MonisRaza123/balloon_driver/images/enclosure2.jpg

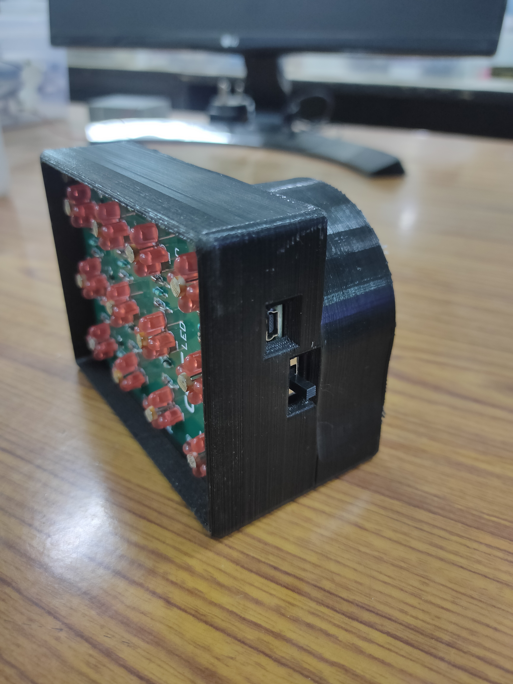
images/enclosure2.jpg
