MonisRaza123/balloon_driver/images/IMG20230621204712.jpg

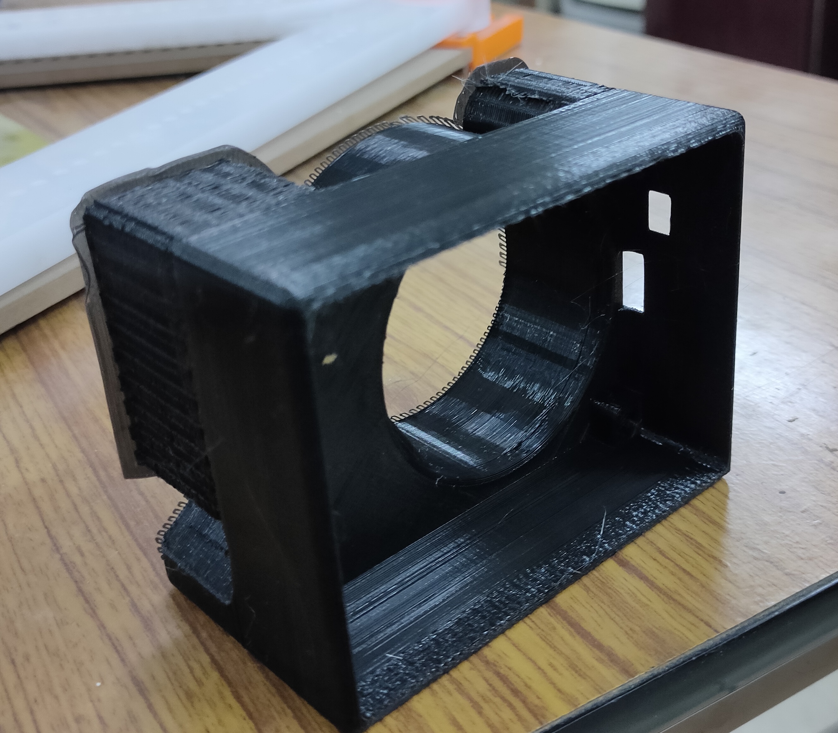
images/IMG20230621204712.jpg
