MonisRaza123/balloon_driver/images/IMG20230621204720.jpg

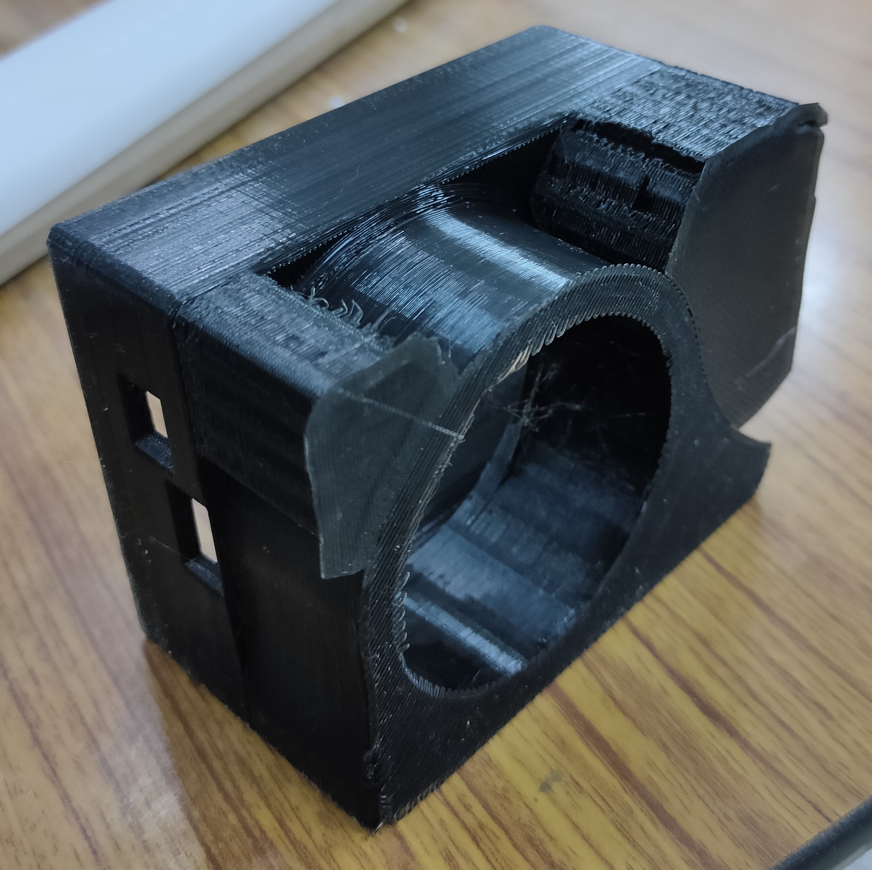
images/IMG20230621204720.jpg
