MonisRaza123/balloon_driver/images/IMG20230703172144.jpg

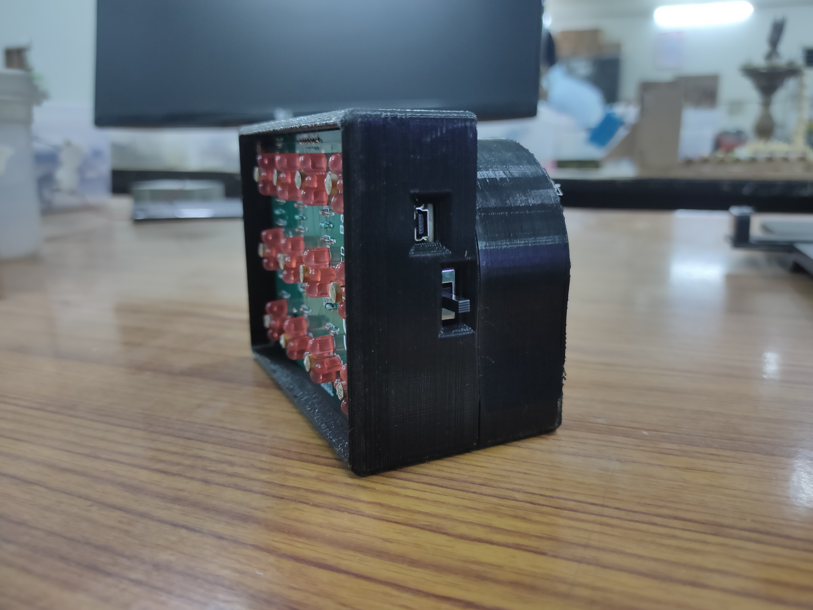
images/IMG20230703172144.jpg
