MonisRaza123/balloon_driver/code/SoundData.h

const unsigned char PROGMEM b1[13798] = {
  0x52, 0x49, 0x46, 0x46, 0xDE, 0x35, 0x00, 0x00, 0x57, 0x41, 0x56, 0x45,
  0x66, 0x6D, 0x74, 0x20, 0x10, 0x00, 0x00, 0x00, 0x01, 0x00, 0x01, 0x00,
  0x80, 0xBB, 0x00, 0x00, 0x80, 0xBB, 0x00, 0x00, 0x01, 0x00, 0x08, 0x00,
  0x64, 0x61, 0x74, 0x61, 0xE8, 0x33, 0x00, 0x00, 0x80, 0x7F, 0x7F, 0x7E,
  0x7F, 0x7F, 0x7E, 0x7F, 0x7E, 0x7F, 0x7E, 0x7E, 0x80, 0x7D, 0x80, 0x7D,
  0x80, 0x80, 0x7D, 0x80, 0x7E, 0x7F, 0x7F, 0x7E, 0x7F, 0x7E, 0x7F, 0x7F,
  0x7E, 0x7F, 0x7D, 0x80, 0x7E, 0x7F, 0x7F, 0x7E, 0x80, 0x7D, 0x80, 0x7E,
  0x7F, 0x80, 0x7D, 0x80, 0x7D, 0x80, 0x7D, 0x7F, 0x7F, 0x7F, 0x7F, 0x7F,
  0x7E, 0x7E, 0x7F, 0x80, 0x7D, 0x80, 0x7E, 0x7F, 0x7F, 0x7E, 0x7F, 0x80,
  0x7D, 0x80, 0x7D, 0x80, 0x7D, 0x80, 0x7E, 0x7F, 0x7F, 0x7E, 0x80, 0x7F,
  0x7E, 0x80, 0x7E, 0x7F, 0x7F, 0x7E, 0x80, 0x7E, 0x80, 0x7E, 0x7F, 0x7F,
  0x7E, 0x80, 0x7D, 0x80, 0x7F, 0x80, 0x7E, 0x7F, 0x7F, 0x7E, 0x7F, 0x7E,
  0x7F, 0x7E, 0x80, 0x7E, 0x7F, 0x7F, 0x7F, 0x80, 0x7E, 0x80, 0x7E, 0x7F,
  0x7E, 0x7F, 0x80, 0x7D, 0x80, 0x7D, 0x80, 0x7E, 0x7F, 0x7F, 0x7F, 0x7F,
  0x80, 0x7F, 0x7F, 0x7F, 0x7E, 0x80, 0x7F, 0x7E, 0x80, 0x7E, 0x80, 0x7E,
  0x80, 0x7D, 0x80, 0x7F, 0x7F, 0x7F, 0x7E, 0x80, 0x7E, 0x7F, 0x7E, 0x7F,
  0x7E, 0x7F, 0x7F, 0x7E, 0x7F, 0x80, 0x7E, 0x7F, 0x7E, 0x7F, 0x7F, 0x7F,
  0x7E, 0x7F, 0x7E, 0x7F, 0x7F, 0x7F, 0x7F, 0x7E, 0x7F, 0x80, 0x7E, 0x80,
  0x7E, 0x80, 0x7E, 0x7F, 0x7E, 0x7F, 0x7E, 0x7E, 0x80, 0x7E, 0x7F, 0x7E,
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
  0x77, 0x7A, 0x89, 0x8A, 0x8B, 0x78, 0x84, 0x81, 0x85, 0x84, 0x75, 0x79,
  0x73, 0x87, 0x78, 0x7F, 0x7D, 0x74, 0x85, 0x7D, 0x93, 0x87, 0x86, 0x85,
  0x7C, 0x91, 0x81, 0x7A, 0x7A, 0x77, 0x82, 0x9A, 0xAD, 0xA4, 0x9B, 0xA9,
  0xB4, 0xB7, 0xA2, 0x8C, 0x75, 0x69, 0x63, 0x73, 0x77, 0x61, 0x79, 0x6A,
  0x69, 0x6D, 0x70, 0x68, 0x4D, 0x55, 0x57, 0x54, 0x4D, 0x33, 0x2A, 0x2C,
  0x25, 0x29, 0x2F, 0x3D, 0x3E, 0x57, 0x50, 0x46, 0x45, 0x3E, 0x51, 0x52,
  0x63, 0x55, 0x55, 0x5B, 0x52, 0x56, 0x5A, 0x5E, 0x70, 0x74, 0x7F, 0x81,
  0x8F, 0x90, 0xA0, 0xA7, 0xAD, 0xAA, 0xA5, 0x99, 0x90, 0x96, 0x86, 0x85,
  0x79, 0x7D, 0x7D, 0x72, 0x6E, 0x56, 0x4D, 0x33, 0x25, 0x20, 0x0D, 0x02,
  0x00, 0x00, 0x00, 0x00, 0x00, 0x00, 0x00, 0x00, 0x00, 0x00, 0x00, 0x00,
  0x00, 0x00, 0x00, 0x00, 0x00, 0x00, 0x00, 0x00, 0x00, 0x00, 0x00, 0x00,
  0x00, 0x00, 0x15, 0x2A, 0x28, 0x52, 0x7D, 0x68, 0x73, 0x77, 0x6B, 0x72,
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
};
